supjj/eddy-Open-Q1/eddy_mount/images/q1_eddy_stable3 (Large).jpg

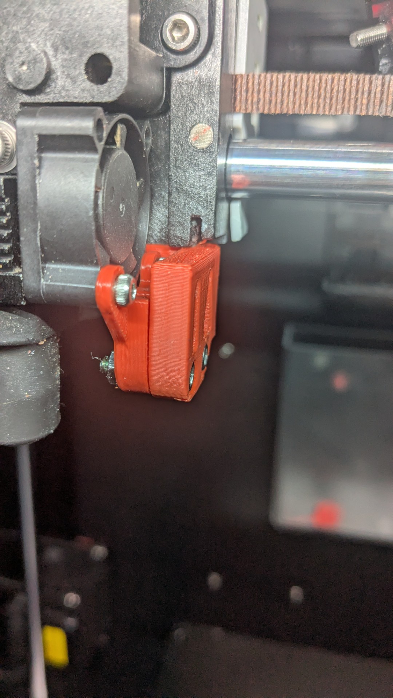
eddy_mount/images/q1_eddy_stable3 (Large).jpg
