supjj/eddy-Open-Q1/eddy_mount/images/q1_pro_eddy_easyalign1 (Large).jpg

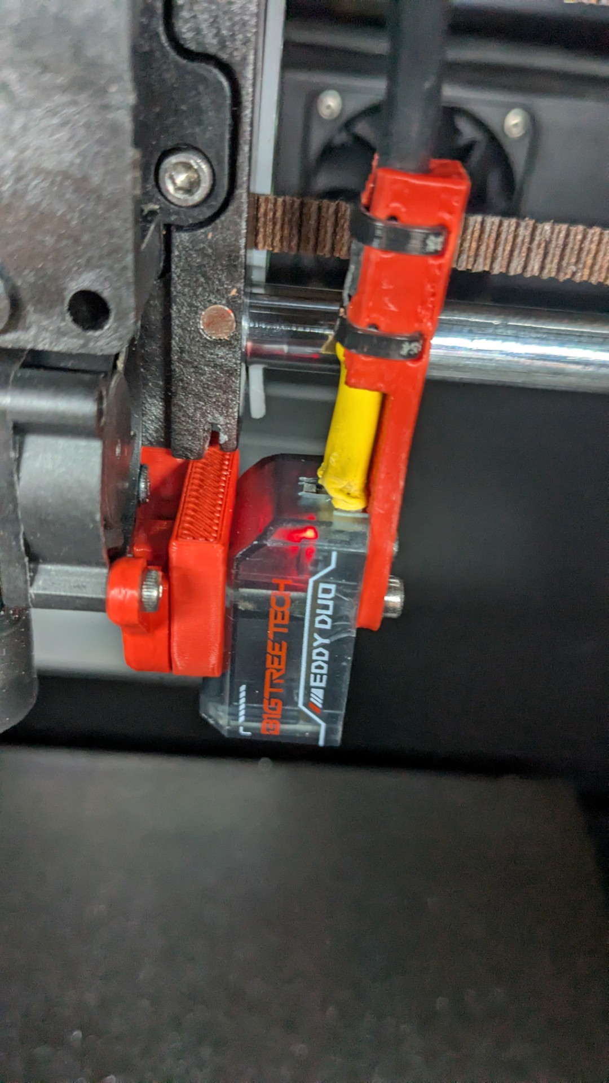
eddy_mount/images/q1_pro_eddy_easyalign1 (Large).jpg
