supjj/eddy-Open-Q1/eddy_mount/images/q1_pro_eddy_easyalign5 (Large).jpg

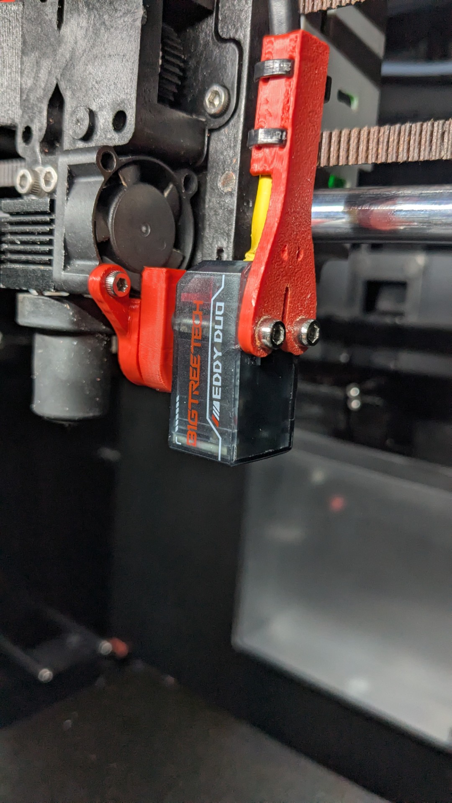
eddy_mount/images/q1_pro_eddy_easyalign5 (Large).jpg
