supjj/eddy-Open-Q1/eddy_mount/easy_align_stable/2mm_inset_base.stl

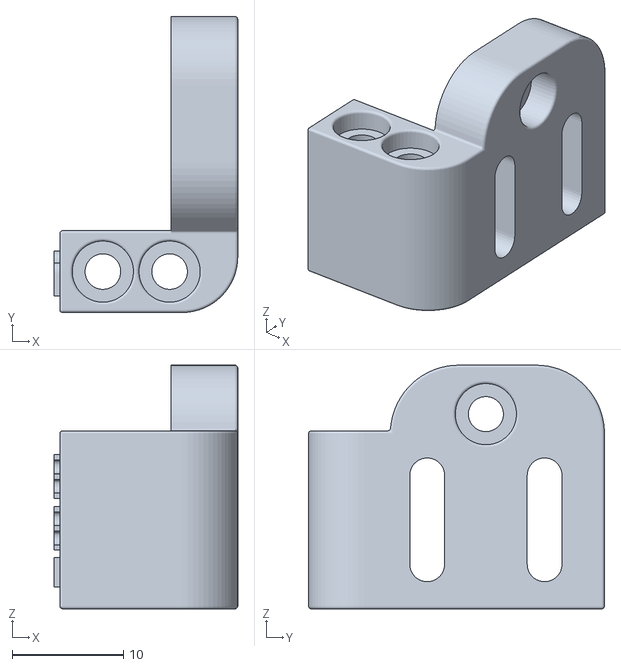
[picture p25: CAD file, 2025-05-13]
eddy_mount/easy_align_stable/2mm_inset_base.stl
16.5 x 26.6 x 21.9
