supjj/eddy-Open-Q1/eddy_mount/stable_eddy/stl/zero_inset.stl

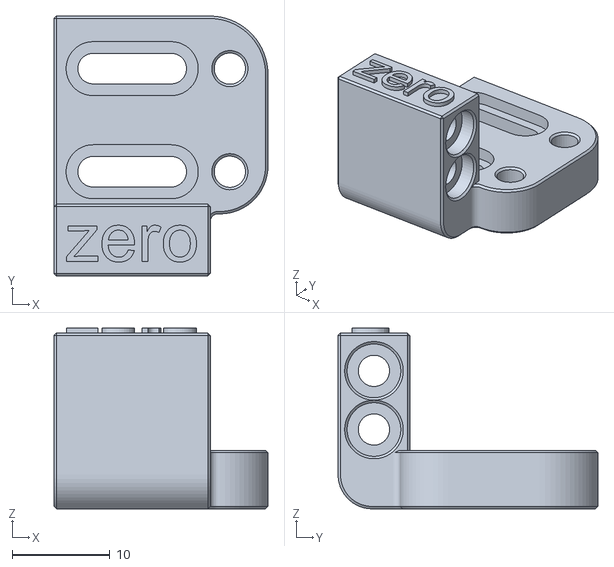
[picture p26: CAD file, 2025-05-10]
eddy_mount/stable_eddy/stl/zero_inset.stl
21.9 x 26.6 x 18.5
