supjj/eddy-Open-Q1/eddy_mount/stable_eddy/stl/ calibration_block_20mm.stl

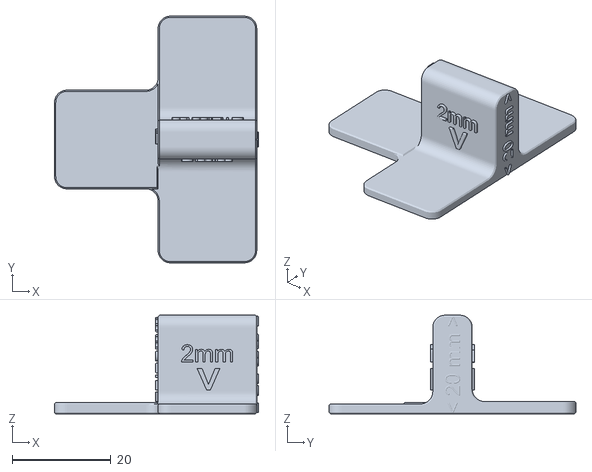
[picture p27: CAD file, 2025-05-10]
eddy_mount/stable_eddy/stl/ calibration_block_20mm.stl
41.4 x 50.0 x 20.0
