supjj/eddy-Open-Q1/config/q1-pro_eddy/homing_override/gcode_macro.cfg

###  https://github.com/straga/3d_printer/tree/master/OpenQ1pro
[gcode_macro PRINT_START]
gcode:

    # Temperature set
    {% set bedtemp = params.BED|int %}
    {% set hotendtemp = params.HOTEND|int %}
    {% set chambertemp = params.CHAMBER|default(0)|int %}
    M140 S{bedtemp}
    M141 S{chambertemp}
    M104 S{hotendtemp * 0.7}

    # Home all axes
    G28
    
    M118 Temperature: Bed: {bedtemp} C, Hotend: {hotendtemp} C, Chamber: {chambertemp} C
    TEMPERATURE_WAIT SENSOR=heater_bed MINIMUM={bedtemp * 0.95} MAXIMUM={bedtemp * 1.05}
    M191 S{chambertemp}

    M118 Go to Clear Nozzle
    #CLEAR_NOZZLE HOTEND=200 COOLDOWN=150 AMOUNT=0
    CLEAR_NOZZLE HOTEND={hotendtemp} COOLDOWN=150

    M118 Go to Home Z
    #G28 Z
    G90
    G1 X{120 - 34} Y{120 - 7} F7800  # Скорректировано с учётом смещения датчика

    M118 Go to Probe
    PROBE_EDDY_NG_TAP

    G28 Z

    M118 Calibrate mesh
    BED_MESH_CALIBRATE PROFILE=adaptive ADAPTIVE=1

    #CLEAR_NOZZLE HOTEND={hotendtemp} COOLDOWN=0 
    M118 Heating
    M109 S{hotendtemp}

    M118 Filament Sensor
    ENABLE_FILAMENT_SENSORS


[gcode_macro PRINT_END]
gcode:
    _RAISE_Z AMOUNT=10  ; drop z by  10 to keep part away from nozzle
    _CLEAR_Z AMOUNT=150 ; drop z to 150 for easy build plate removal

    G1 X0 Y0 F7800

    CLEAR_PAUSE

    DISABLE_FANS_AND_HEATERS

    M220 S100 #reset speed factor
    M221 S100 #reset extrude factor
    
    PROBE_EDDY_NG_SET_TAP_OFFSET VALUE=0
    BED_MESH_CLEAR

    M84

    DISABLE_FILAMENT_SENSORS
    BEEP I=2 DUR=500

# DO NOT EDIT THIS FILE.
# This file is part of a git repository, your changes may prevent updates
[gcode_macro _SET_ACCEL]
gcode:
    {% set printer_config = printer.configfile.settings['printer'] %}
    {% set s = params.ACCEL|default(printer_config.max_accel)|float %}
    SET_VELOCITY_LIMIT ACCEL={s}

[gcode_macro _RAISE_Z]
description: Drop the bed by AMOUNT to prevent dragging
gcode:
    {% set curr_z = printer.toolhead.position.z %}
    {% set max_z = printer.toolhead.axis_maximum.z %}
    {% set target_z = curr_z + params.AMOUNT|default(10)|float %}

    G90 ; absolute
    G1 Z { [target_z, max_z]|min }

[gcode_macro _CLEAR_Z]
description: Drop Z by at least up to AMOUNT to leave room for stuff
gcode:
    {% set curr_z = printer.toolhead.position.z %}
    {% set max_z = printer.toolhead.axis_maximum.z %}
    {% set target_z = [curr_z, params.AMOUNT|default(10)|float]|max %}

    G90 ; absolute
    G1 Z { [target_z, max_z]|min }

[gcode_macro GO_TO_BUCKET]
description: Go to purge bucket position for filament unload or purging
gcode:
    SAVE_VARIABLE VARIABLE=at_bucket VALUE=True
    _CLEAR_Z AMOUNT=30

    G90 ; absolute

    {% set curr_y = printer.toolhead.position.y %}
    {% if curr_y > 240 %} ; prevent crash from rear
        G1 Y240 F9000
    {% endif %}

    G1 X94 Y240 F9000
    _SET_ACCEL ACCEL=100
    G1 Y254 F1500 ; gently press against wiper arm
    _SET_ACCEL ; reset accel

[gcode_macro LEAVE_BUCKET]
description: Leave the bucket gracefully
gcode:
    SAVE_VARIABLE VARIABLE=at_bucket VALUE=False
    {% set curr_x = printer.toolhead.position.x %}
    {% set curr_y = printer.toolhead.position.y %}
    {% if (curr_y >= 240) and (curr_x >= 59) and (curr_x <= 98) %}
        G90 ; absolute
        _SET_ACCEL ACCEL=500
        G1 Y254 F2000
        G1 X70 F5000
        _SET_ACCEL ACCEL=100
        G1 Y240 F1500 ; gently leave the wiper arm
        _SET_ACCEL ; reset accel
    {% endif %}

[gcode_macro _BUCKET_CUT]
description: Cut off the extruded filament on the nozzle
gcode:
    {% set i = 6 %}
    {% for iteration in range(i|int) %}
        G1 X85 F2000
        G1 X94  F2000
    {% endfor %}

[gcode_macro _FELT_WIPE]
description: Wipe on the felt pad
gcode:
    G90 ; absolute
    ; felt is roughly X60-88 (88 is the "cutter" end), Y254-250

    {% set random_x = (range(0, 100) | random) / 10 %}
    {% set X_end = 60 + random_x %}

    {% set random_y = (range(0, 30) | random) / 10 %}
    {% set Y_end = 254 - random_y %}
    G1 Y{Y_end} F1500

    {% set i = 3 %}
    {% for iteration in range(i|int) %}
        G1 X88 F500
        G1 X{X_end} F500
    {% endfor %}

    {% for iteration in range(i|int) %}
        G1 Y249 F500
        G1 Y{Y_end} F500
    {% endfor %}

    {% for iteration in range(i|int) %}
        G1 X88 F500
        G1 X{X_end} F500
    {% endfor %}


[gcode_macro _BUCKET_PURGE]
description: Purge filament to the purge bucket
gcode:
    M118 Purging

    {% set hotendtemp = params.HOTEND|default(250)|int %}
    M104 S{hotendtemp}

    GO_TO_BUCKET

    ; Wait for extruder to be +/- 5% of target
    TEMPERATURE_WAIT SENSOR=extruder MINIMUM={hotendtemp * 0.95} MAXIMUM={hotendtemp * 1.05}

    {% set purgeamount = params.AMOUNT|default(80)|int %}
    M83 ; relative E
    G92 E0 ; reset E
    G1 E{purgeamount} F400 ; extrude
    G1 E-1 F400 ; retract

    M106 S255 ; cooling fan max
    G4 P5000 ; wait for 5 seconds
    M106 S0 ; cooling fan off

    _BUCKET_CUT
    {% set leave = params.LEAVE|default(1)|int %}
    {% if leave > 0 %}
        LEAVE_BUCKET
    {% endif %}


[gcode_macro CLEAR_NOZZLE]
gcode:
    {% set hotendtemp = params.HOTEND|default(250)|int %}
    {% set purgeamount = params.AMOUNT|default(80)|int %}
    {% set cool_nozzle = params.COOLDOWN|default(1)|int %}

    _BUCKET_PURGE HOTEND={hotendtemp} AMOUNT={purgeamount} LEAVE={0} ; purge without leaving

    {% if cool_nozzle > 0 %}
        M104 S0 ; shut down extruder
    {% endif %}
    _FELT_WIPE
    M400
    M118 Nozzle cleared

    LEAVE_BUCKET ; gracefully leave the bucket

    {% if cool_nozzle > 0 %}
        G1 Y120 F9000
        G1 X222 F9000
        SET_FAN_SPEED FAN=auxiliary_cooling_fan SPEED=1
        SET_FAN_SPEED FAN=cooling_fan SPEED=1
        TEMPERATURE_WAIT SENSOR=extruder MAXIMUM={hotendtemp * 0.8}
        M118 Nozzle cooled
        SET_FAN_SPEED FAN=auxiliary_cooling_fan SPEED=0
        SET_FAN_SPEED FAN=cooling_fan SPEED=0
    {% endif %}

    M107
    M106 P2 S0
    M400

#[gcode_macro PRINT_START]
#gcode:
#    SET_FAN_SPEED FAN=board_fan SPEED=0.5
#    # Load Z offset, cancel if none is set
#    {% set gcode_offset = printer.gcode_move.homing_origin.z|float %}
#    {% set auto_z_offset = printer.configfile.config.auto_z_offset.calibrated_z_offset|float %}
#    {% if gcode_offset == 0.0 %}
#        AUTO_Z_LOAD_OFFSET
#        {% if auto_z_offset == 0.0 %}
#            _ERROR MSG="No gcode offset detected! Run AUTO_Z_CALIBRATE before starting a print to ensure a good first layer."
#        {% endif %}
#    {% endif %}
#
#    {% set bedtemp = params.BED|int %}
#    {% set hotendtemp = params.HOTEND|int %}
#    {% set chambertemp = params.CHAMBER|default(0)|int %}
#    M140 S{bedtemp}
#    M141 S{chambertemp}
#   M104 S{hotendtemp * 0.7}
#    G28

#    TEMPERATURE_WAIT SENSOR=heater_bed MINIMUM={bedtemp * 0.95} MAXIMUM={bedtemp * 1.05}
#    BED_MESH_CALIBRATE PROFILE=adaptive ADAPTIVE=1
#    M191 S{chambertemp}
#    CLEAR_NOZZLE HOTEND={hotendtemp} COOLDOWN=0
#    M109 S{hotendtemp}

#    ENABLE_FILAMENT_SENSORS

[gcode_macro ENABLE_FILAMENT_SENSORS]
gcode:
    ENABLE_FILAMENT_WIDTH_SENSOR
    RESET_FILAMENT_WIDTH_SENSOR
    query_filament_width
    SET_FILAMENT_SENSOR SENSOR=tangle ENABLE=1

[gcode_macro DISABLE_FILAMENT_SENSORS]
gcode:
    SET_FILAMENT_SENSOR SENSOR=tangle ENABLE=0
    DISABLE_FILAMENT_WIDTH_SENSOR

[homing_override]
axes:xyz
gcode:
    {% set HOME_CUR = 0.6 %}
    {% set driver_config = printer.configfile.settings['tmc2240 stepper_x'] %}
    {% set RUN_CUR = driver_config.run_current %}
    {% set HOME_X = params.X %}
    {% set HOME_Y = params.Y %}
    {% set HOME_Z = params.Z %}
    M204 S10000
    {% if (HOME_X is undefined) and (HOME_Y is undefined) and (HOME_Z is undefined) %}
        {% set HOME_X = 1 %}
        {% set HOME_Y = 1 %}
        {% set HOME_Z = 1 %}
        {% set HOME_ALL = 1 %}

        SET_KINEMATIC_POSITION Z={printer.toolhead.axis_maximum.z-10}
        G91
        G1 Z5 F600
        {% if printer.save_variables.variables.at_bucket %}
            SET_KINEMATIC_POSITION X=70
            SET_KINEMATIC_POSITION Y=254
            LEAVE_BUCKET
        {% else %}
            SET_KINEMATIC_POSITION X=0
            SET_KINEMATIC_POSITION Y=0
            G1 X10 F2400
            G1 Y10 F2400
        {% endif %}
        G4 P2000
    {% endif %}

    {% if HOME_Y is defined %}
        SET_TMC_CURRENT STEPPER=stepper_y CURRENT={HOME_CUR}
        G28 Y
        SET_TMC_CURRENT STEPPER=stepper_y CURRENT={RUN_CUR}
        BEEP I=1 DUR=100
        G1 Y10 F1200
    {% endif %}

    {% if HOME_X is defined %}
        SET_TMC_CURRENT STEPPER=stepper_x CURRENT={HOME_CUR}
        G28 X
        SET_TMC_CURRENT STEPPER=stepper_x CURRENT={RUN_CUR}
        BEEP I=1 DUR=100
        G1 X10 F1200
    {% endif %}

    {% if HOME_Z is defined %}
        G90
        G1 X120 Y120 F7800
        G91
        G28 Z

        {% if not printer.z_tilt.applied %}
            Z_TILT_ADJUST
        {% endif %}

        G90
        G1 X120 Y120 F7800
        G1 Z10 F600
    {% endif %}

    M204 S10000
    G90

[gcode_macro SHAPER_CALIBRATE]
rename_existing: RESHAPER_CALIBRATE
gcode:
    RESHAPER_CALIBRATE FREQ_START=20 FREQ_END=150

[gcode_macro DISABLE_FANS_AND_HEATERS]
gcode:
    M106 P2 S0
    M106 P0 S0
    M106 P3 S0

    M104 S0
    M140 S0
    M141 S0

#[gcode_macro PRINT_END]
#gcode:
#    _RAISE_Z AMOUNT=10  ; drop z by  10 to keep part away from nozzle
#    _CLEAR_Z AMOUNT=150 ; drop z to 150 for easy build plate removal
#
#    G1 X0 Y0 F7800
#
#    CLEAR_PAUSE
#
#    DISABLE_FANS_AND_HEATERS
#
#    M220 S100 #reset speed factor
#    M221 S100 #reset extrude factor
#
#    M84
#
#    DISABLE_FILAMENT_SENSORS
#    BEEP I=2 DUR=500

[gcode_macro CANCEL_PRINT]
rename_existing: BASE_CANCEL_PRINT
gcode:
    PRINT_END
    BASE_CANCEL_PRINT

[gcode_macro PAUSE]
rename_existing: BASE_PAUSE
gcode:
    # Parameters
    {% set z = params.Z|default(35)|int %}                                                   ; z hop amount

    {% if printer['pause_resume'].is_paused|int == 0 %}
        SET_GCODE_VARIABLE MACRO=RESUME VARIABLE=zhop VALUE={z}                              ; set z hop variable for reference in resume macro
        SET_GCODE_VARIABLE MACRO=RESUME VARIABLE=etemp VALUE={printer['extruder'].target}    ; set hotend temp variable for reference in resume macro

        DISABLE_FILAMENT_SENSORS
        SAVE_GCODE_STATE NAME=PAUSE                                                          ; save current print position for resume
        BASE_PAUSE                                                                           ; pause print
        {% if (printer.gcode_move.position.z ) < z %}                                        ; check that zhop doesn't exceed z max
            G91                                                                              ; relative positioning
            G1 Z{z} F900                                                                     ; raise Z up by z hop amount
        {% else %}
            G91                                                                              ; relative positioning
            G1 Z{5} F900
            SET_GCODE_VARIABLE MACRO=RESUME VARIABLE=zhop VALUE=0
        {% endif %}
        SAVE_GCODE_STATE NAME=PAUSEPARK2
        G90                                                                                  ; absolute positioning
        G1 X94  F9000
        G1 Y253 F9000                                     ; park toolhead at front center
        SAVE_GCODE_STATE NAME=PAUSEPARK                                                      ; save parked position in case toolhead is moved during the pause (otherwise the return zhop can error)
        M104 S0                                                                              ; turn off hotend
        SET_STEPPER_ENABLE STEPPER=extruder enable=0
    {% endif %}

[gcode_macro RESUME]
rename_existing: BASE_RESUME
variable_zhop: 0
variable_etemp: 0
gcode:
    # Parameters
    {% set e = params.E|default(5)|int %}                                          ; hotend prime amount (in mm)

    {% if printer['pause_resume'].is_paused|int == 1 %}
        {% if etemp > 0 %}
            M109 S{etemp|int}                                                        ; wait for hotend to heat back up
        {% endif %}
        M83                                                                          ; relative extruder positioning
        G1 X94   F9000
        G1 Y253 F9000
        G91
        G1  E{e} F300                                                ; prime nozzle by E, lower Z back down
        G90
        CLEAR_NOZZLE HOTEND={etemp|int} COOLDOWN=0
        G1 Y200 F3000
        RESTORE_GCODE_STATE NAME=PAUSEPARK2 MOVE=1 MOVE_SPEED=200
        RESTORE_GCODE_STATE NAME=PAUSE MOVE=1 MOVE_SPEED=10                         ; restore position
        BASE_RESUME
        ENABLE_FILAMENT_SENSORS
    {% endif %}

[gcode_macro BEEP]
gcode:
    # Parameters
    {% set i = params.I|default(1)|int %}        ; Iterations (number of times to beep).
    {% set dur = params.DUR|default(100)|int %}  ; Duration/wait of each beep in ms. Default 100ms.

    {% if printer["output_pin sound"].value|int == 1 %}
        {% for iteration in range(i|int) %}
            SET_PIN PIN=beeper VALUE=1
            G4 P{dur}
            SET_PIN PIN=beeper VALUE=0
            G4 P{dur}
        {% endfor %}
    {% endif %}

[gcode_macro M141]
description: set chamber heater temperature
gcode:
    {% set s = params.S|float %}
    SET_HEATER_TEMPERATURE HEATER=chamber TARGET={([s, 60]|min)}

[gcode_macro M191]
description: wait for chamber to reach temperature
gcode:
    #Parameters
    {% set s = params.S|float %}

    M141 {% for p in params %}{'%s%s' % (p, params[p])}{% endfor %}
    {% if s != 0 %}
        TEMPERATURE_WAIT SENSOR="heater_generic chamber" MINIMUM={([s, 60]|min)-2} #MAXIMUM={s+1}
    {% endif %}

[gcode_macro M106]
description: set fan speed (aux/cooling/circulation)
gcode:
    {% set p = params.P|default(0)|int %}

    {% if p == 2 %}
    {% if params.S is defined %}
        SET_FAN_SPEED FAN=auxiliary_cooling_fan SPEED={(params.S|float / 255.0)}
    {% else %}
        SET_FAN_SPEED FAN=auxiliary_cooling_fan SPEED=1
    {% endif %}
    {% endif %}

    {% if p == 0 %}
    {% if params.S is defined %}
        SET_FAN_SPEED FAN=cooling_fan SPEED={(params.S|float / 255.0)}
    {% else %}
        SET_FAN_SPEED FAN=cooling_fan SPEED=1
    {% endif %}
    {% endif %}

    {% if p == 3 %}
    {% if params.S is defined %}
        SET_FAN_SPEED FAN=chamber_circulation_fan SPEED={(params.S|float / 255.0)}
    {% else %}
        SET_FAN_SPEED FAN=chamber_circulation_fan SPEED=1
    {% endif %}
    {% endif %}

[gcode_macro M107]
description: stop cooling fan speed
gcode:
    SET_FAN_SPEED FAN=cooling_fan SPEED=0

[gcode_macro M603]
description: Filament unload
gcode:
    GO_TO_BUCKET
    M118 Heat up complete
    TIP_FORMING
    G1  E-90 F3000
    _BUCKET_CUT
    M400
    M118 Unload finish
    LEAVE_BUCKET

[gcode_macro M604]
description: Filament load
gcode:
    GO_TO_BUCKET
    M118 Heat up complete
    M83 # relative extruder positioning
    _BUCKET_PURGE AMOUNT=80
    M400
    M118 Load finish
    LEAVE_BUCKET

[gcode_macro M109]
rename_existing: M99109
gcode:
    #Parameters
    {% set s = params.S|float %}

    M104 {% for p in params %}{'%s%s' % (p, params[p])}{% endfor %}  ; Set hotend temp
    {% if s != 0 %}
        TEMPERATURE_WAIT SENSOR=extruder MINIMUM={s} MAXIMUM={s+1}   ; Wait for hotend temp (within 1 degree)
    {% endif %}

[gcode_macro M204]
rename_existing: M99204
gcode:
    {% if params.S is defined %}
        {% set s = params.S|float %}
    {% endif %}
    {% if params.P is defined %}
    {% if params.T is defined %}
        {% set s = [params.P|float ,params.T|float] | min %}
    {% endif %}
    {% endif %}

    SET_VELOCITY_LIMIT ACCEL={s}
    SET_VELOCITY_LIMIT ACCEL_TO_DECEL={s/2}

[gcode_macro _ERROR]
gcode:
    {% set err = params.MSG|string %}
    M118 {err}
    CANCEL_PRINT

[gcode_macro TIP_FORMING]  # from RatRig RatOS
gcode:
    # cooling parameter
	{% set cooling_moves = params.COOLING_MOVES|default(4)|int %}
	{% set cooling_move_length = params.COOLING_MOVE_LENGTH|default(10)|float %}
	{% set start_cooling_speed = params.START_COOLING_SPEED|default(10)|float * 60 %}
	{% set end_cooling_speed = params.END_COOLING_SPEED|default(50)|float * 60 %}
	{% if cooling_moves == 0 %}
		{% set cooling_move_length = 0 %}
	{% endif %}

	# dipping parameter
	{% set dip = true if params.DIP|default(false)|lower == "true" else false %}
	{% set dip_length = params.DIP_LENGTH|default(22)|float %}
	{% set dip_speed = params.DIP_SPEED|default(30)|float * 60 %}
	{% set dip_retract_speed = params.DIP_RETRACT_SPEED|default(70)|float * 60 %}

	# retraction parameter
	{% set retract_length = params.RETRACT_LENGTH|default(18)|float %}
	{% set start_retract_speed = params.START_RETRACT_SPEED|default(120)|float * 60 %}
	{% set end_retract_speed = params.END_RETRACT_SPEED|default(20)|float * 60 %}

	M220 S100    # reset any speed override

	# retraction
	G92 E0       # Reset extrusion distance
	{% set retract = retract_length + cooling_move_length / 2 - 15 %}
	G1 E-15 F{start_retract_speed}
	G1 E-{0.7 * retract} F{1.0 * end_retract_speed}
	G1 E-{0.2 * retract} F{0.5 * end_retract_speed}
	G1 E-{0.1 * retract} F{0.3 * end_retract_speed}

	# cooling
	G92 E0       # Reset extrusion distance
	{% if cooling_moves > 0 %}
		{% set i = (end_cooling_speed - start_cooling_speed) / (2 * cooling_moves - 1) %}
		{% for m in range(cooling_moves) %}
			G1 E{cooling_move_length} F{(start_cooling_speed + i * m * 2)}
			G1 E-{cooling_move_length} F{(start_cooling_speed + i * (m * 2 + 1))}
		{% endfor %}
	{% endif %}

	# dipping
	G92 E0       # Reset extrusion distance
	{% if dip %}
		G1 E{dip_length} F{dip_speed}
		G4 P100
		G1 E-{dip_length} F{dip_retract_speed}
	{% endif %}

	G92 E0      # Reset extrusion distance
	M400        # Wait for moves to finish
